sonocircuit/EXIST-RIP/EXIST Images/IMG_2364.jpg

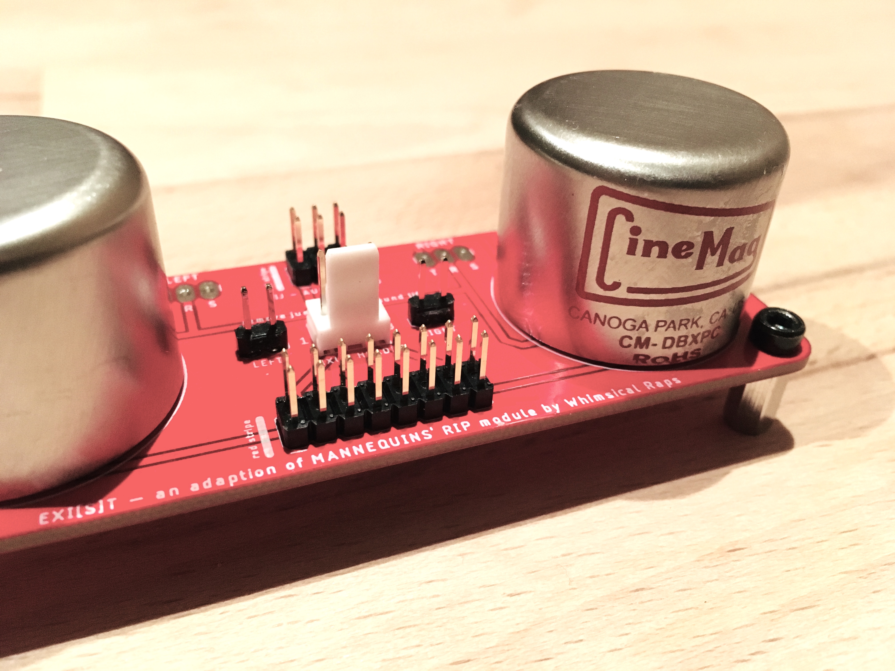
EXIST Images/IMG_2364.jpg
