sonocircuit/EXIST-RIP/EXIST Images/IMG_2365.jpg

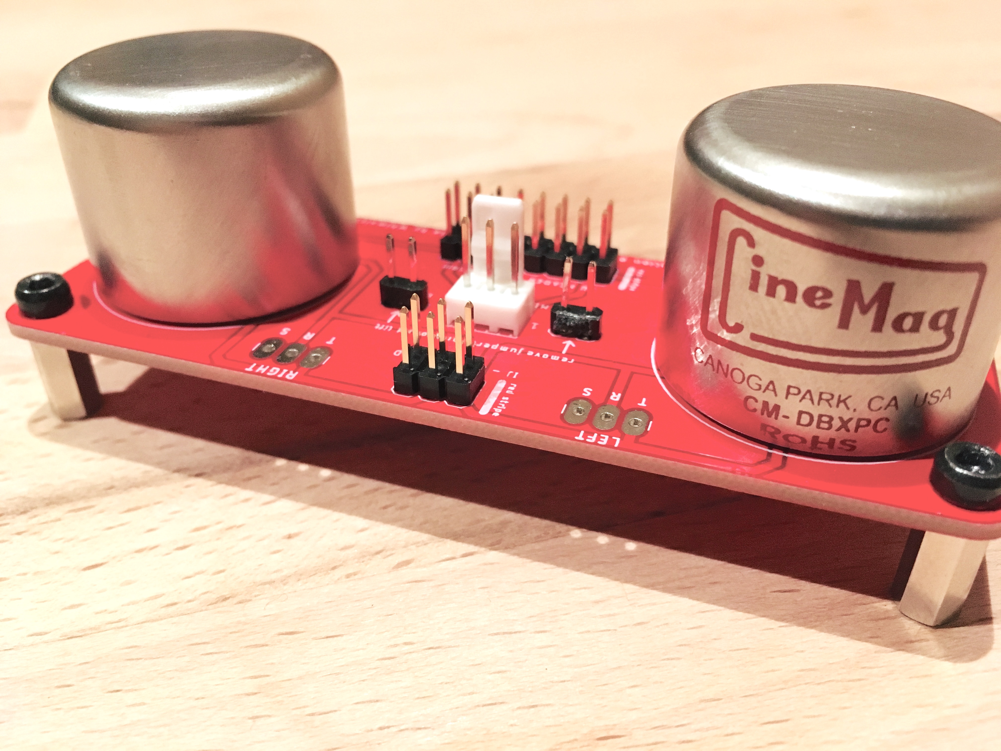
EXIST Images/IMG_2365.jpg
