sonocircuit/EXIST-RIP/EXIST Images/IMG_2367.jpg

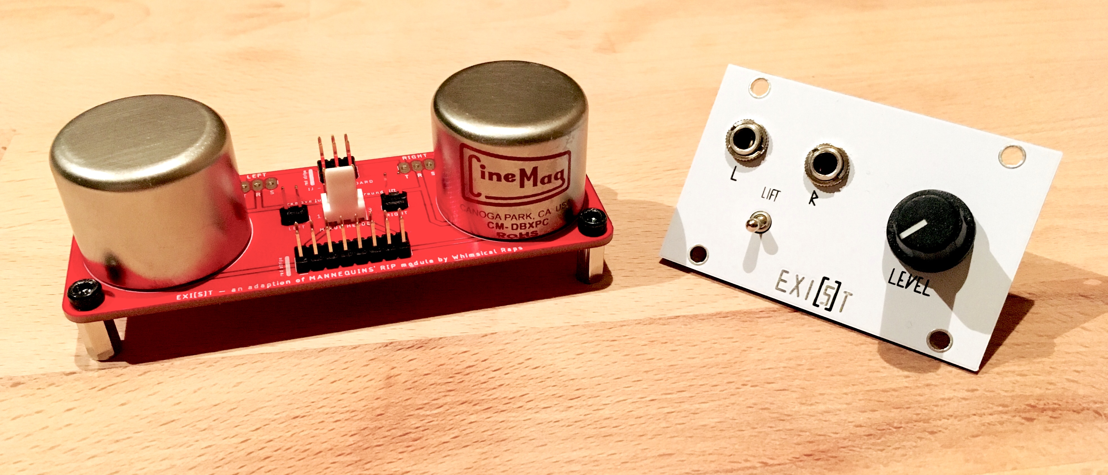
EXIST Images/IMG_2367.jpg
