sonocircuit/EXIST-RIP/EXIST Images/IMG_2369.jpg

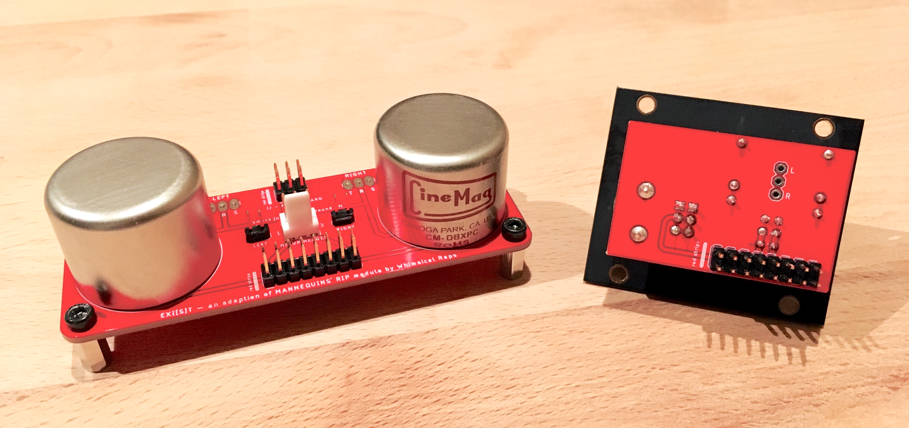
EXIST Images/IMG_2369.jpg
